ChristianIannella/MicroKeyboard/Docs/1.jpg

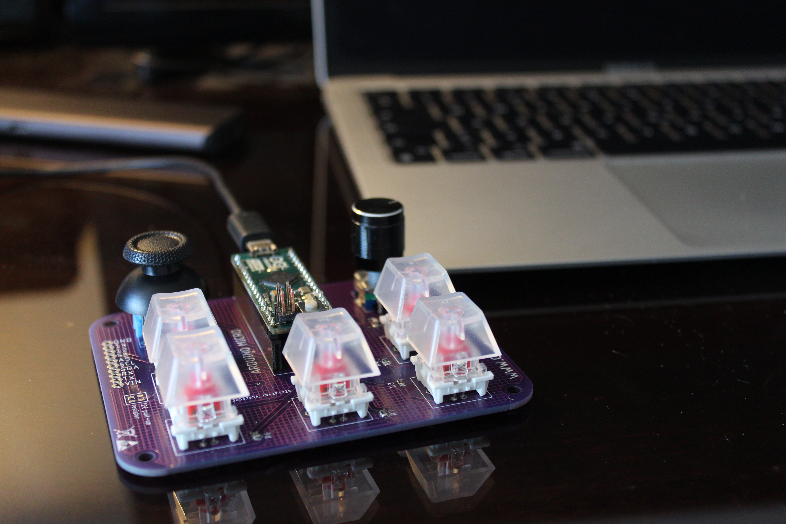
Docs/1.jpg
