ChristianIannella/MicroKeyboard/Docs/2.jpg

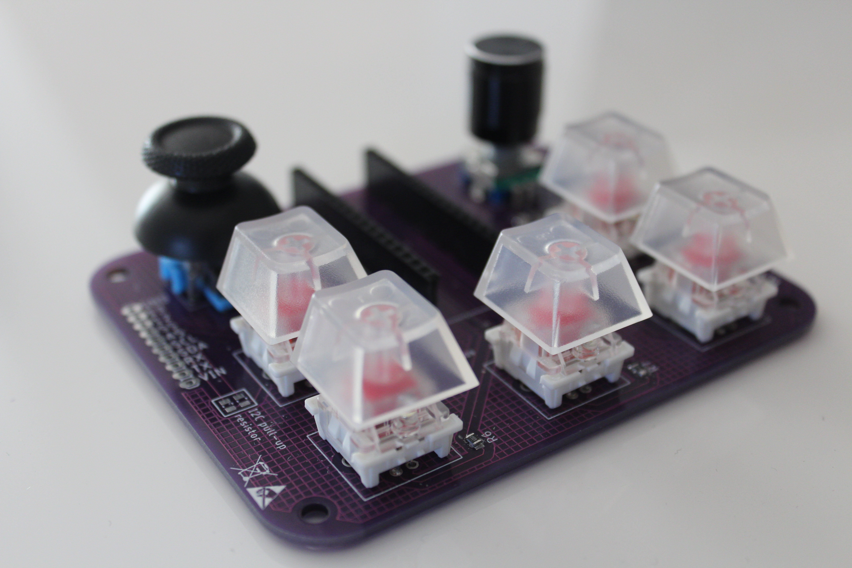
Docs/2.jpg
