ChristianIannella/MicroKeyboard/Docs/3.jpg

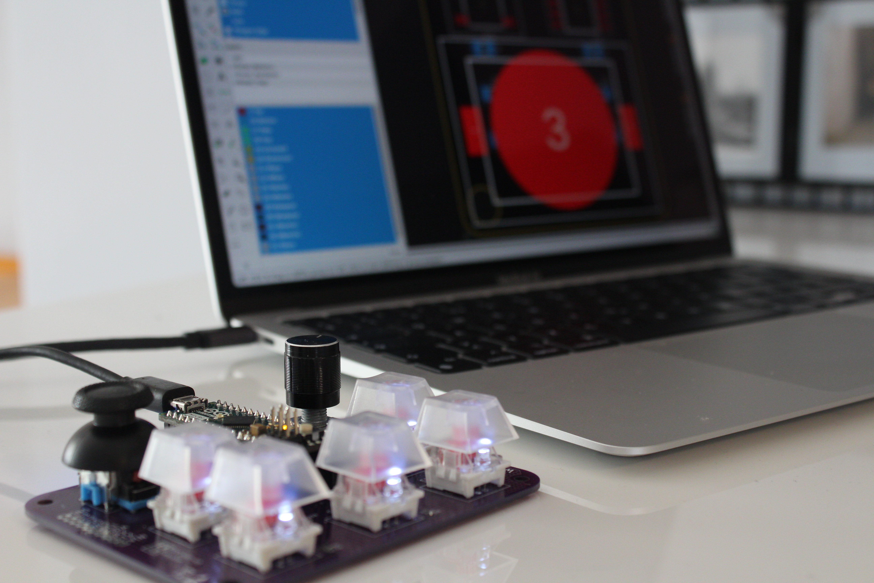
Docs/3.jpg
