ChristianIannella/MicroKeyboard/Docs/4.jpg

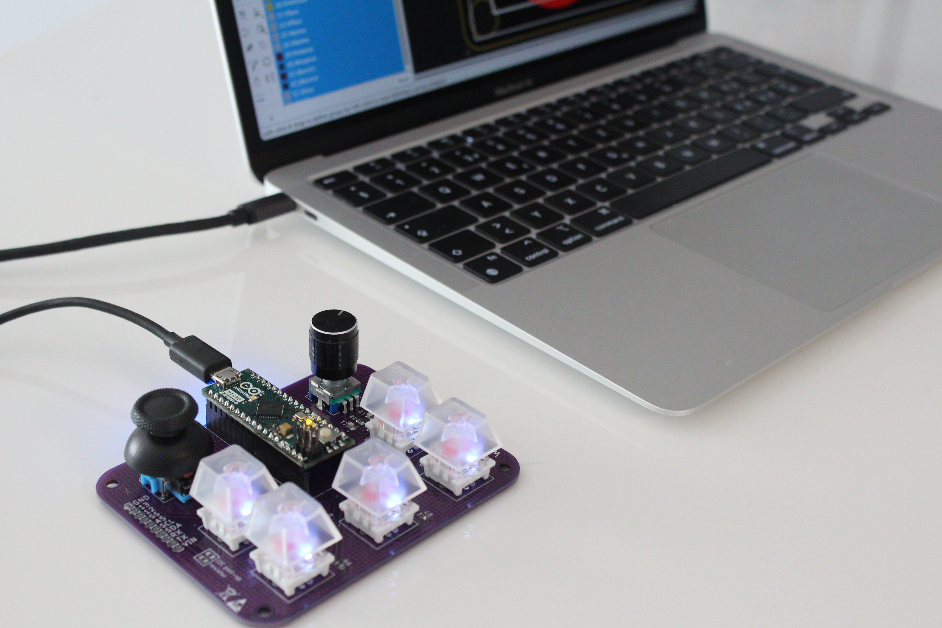
Docs/4.jpg
