ChristianIannella/MicroKeyboard/Docs/6.jpg

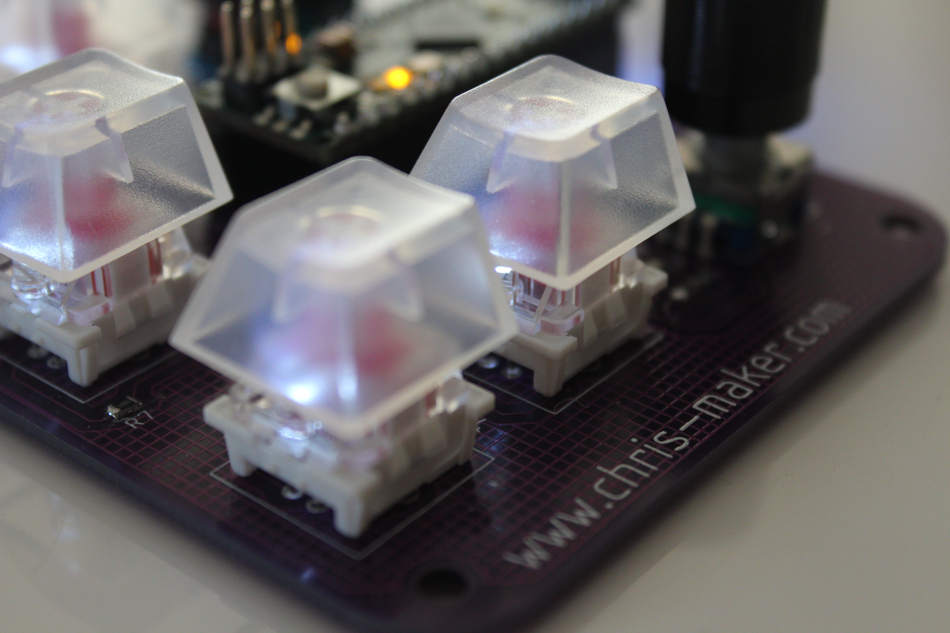
Docs/6.jpg
