ChristianIannella/MicroKeyboard/Docs/8.png

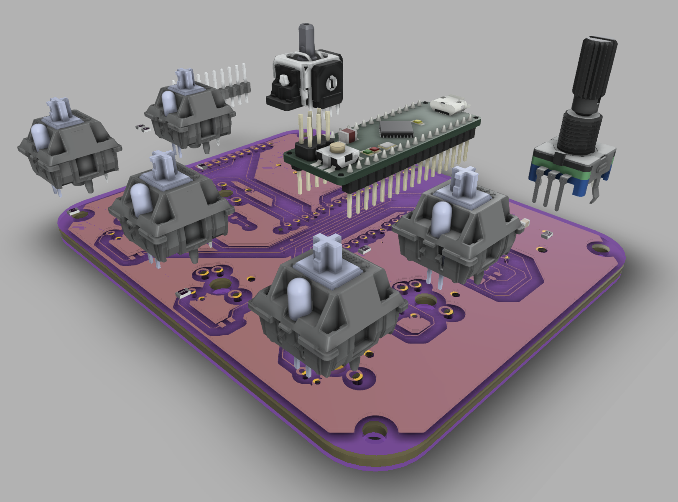
Docs/8.png
